dynamix/lolly/firmware/src/palette.h

TBlendType currentBlending;

uint8_t currentPaletteNumber = 0;
CRGBPalette16 currentPalette(CRGB::Black);
CRGBPalette16 targetPalette;

extern CRGBPalette16 myRedWhiteBluePalette;
extern const TProgmemPalette16 myRedWhiteBluePalette_p PROGMEM;

// This function fills the palette with totally random colors.
void SetupTotallyRandomPalette()
{
  for (int i = 0; i < 16; i++)
  {
    currentPalette[i] = CHSV(random8(), 255, random8());
  }
}

// This function sets up a palette of black and white stripes,
// using code.  Since the palette is effectively an array of
// sixteen CRGB colors, the various fill_* functions can be used
// to set them up.
void SetupBlackAndWhiteStripedPalette()
{
  // 'black out' all 16 palette entries...
  fill_solid(currentPalette, 16, CRGB::Black);
  // and set every fourth one to white.
  currentPalette[0] = CRGB::White;
  currentPalette[4] = CRGB::White;
  currentPalette[8] = CRGB::White;
  currentPalette[12] = CRGB::White;
}

// This function sets up a palette of purple and green stripes.
void SetupPurpleAndGreenPalette()
{
  CRGB purple = CHSV(HUE_PURPLE, 255, 255);
  CRGB green = CHSV(HUE_GREEN, 255, 255);
  CRGB black = CRGB::Black;

  currentPalette = CRGBPalette16(
      green, green, black, black,
      purple, purple, black, black,
      green, green, black, black,
      purple, purple, black, black);
}

void ChangePalettePeriodically()
{
  uint8_t secondHand = (millis() / 1000) % 60;
  static uint8_t lastSecond = 99;

  if (lastSecond != secondHand)
  {
    lastSecond = secondHand;
    if (secondHand == 0)
    {
      currentPalette = RainbowColors_p;
      currentBlending = LINEARBLEND;
    }
    if (secondHand == 10)
    {
      currentPalette = RainbowStripeColors_p;
      currentBlending = NOBLEND;
    }
    if (secondHand == 15)
    {
      currentPalette = RainbowStripeColors_p;
      currentBlending = LINEARBLEND;
    }
    if (secondHand == 20)
    {
      SetupPurpleAndGreenPalette();
      currentBlending = LINEARBLEND;
    }
    if (secondHand == 25)
    {
      SetupTotallyRandomPalette();
      currentBlending = LINEARBLEND;
    }
    if (secondHand == 30)
    {
      SetupBlackAndWhiteStripedPalette();
      currentBlending = NOBLEND;
    }
    if (secondHand == 35)
    {
      SetupBlackAndWhiteStripedPalette();
      currentBlending = LINEARBLEND;
    }
    if (secondHand == 40)
    {
      currentPalette = CloudColors_p;
      currentBlending = LINEARBLEND;
    }
    if (secondHand == 45)
    {
      currentPalette = PartyColors_p;
      currentBlending = LINEARBLEND;
    }
  }
}

// Gradient Color Palette definitions for 33 different cpt-city color palettes.
//     956 bytes of PROGMEM for all of the palettes together,
//    +618 bytes of PROGMEM for gradient palette code (AVR).
//   1,494 bytes total for all 34 color palettes and associated code.

// Gradient palette "ib_jul01_gp", originally from
// http://soliton.vm.bytemark.co.uk/pub/cpt-city/ing/xmas/tn/ib_jul01.png.index.html
// converted for FastLED with gammas (2.6, 2.2, 2.5)
// Size: 16 bytes of program space.

DEFINE_GRADIENT_PALETTE(ib_jul01_gp){
    0, 194, 1, 1,
    94, 1, 29, 18,
    132, 57, 131, 28,
    255, 113, 1, 1};

// Gradient palette "es_vintage_57_gp", originally from
// http://soliton.vm.bytemark.co.uk/pub/cpt-city/es/vintage/tn/es_vintage_57.png.index.html
// converted for FastLED with gammas (2.6, 2.2, 2.5)
// Size: 20 bytes of program space.

DEFINE_GRADIENT_PALETTE(es_vintage_57_gp){
    0, 2, 1, 1,
    53, 18, 1, 0,
    104, 69, 29, 1,
    153, 167, 135, 10,
    255, 46, 56, 4};

// Gradient palette "es_vintage_01_gp", originally from
// http://soliton.vm.bytemark.co.uk/pub/cpt-city/es/vintage/tn/es_vintage_01.png.index.html
// converted for FastLED with gammas (2.6, 2.2, 2.5)
// Size: 32 bytes of program space.

DEFINE_GRADIENT_PALETTE(es_vintage_01_gp){
    0, 4, 1, 1,
    51, 16, 0, 1,
    76, 97, 104, 3,
    101, 255, 131, 19,
    127, 67, 9, 4,
    153, 16, 0, 1,
    229, 4, 1, 1,
    255, 4, 1, 1};

// Gradient palette "es_rivendell_15_gp", originally from
// http://soliton.vm.bytemark.co.uk/pub/cpt-city/es/rivendell/tn/es_rivendell_15.png.index.html
// converted for FastLED with gammas (2.6, 2.2, 2.5)
// Size: 20 bytes of program space.

DEFINE_GRADIENT_PALETTE(es_rivendell_15_gp){
    0, 1, 14, 5,
    101, 16, 36, 14,
    165, 56, 68, 30,
    242, 150, 156, 99,
    255, 150, 156, 99};

// Gradient palette "rgi_15_gp", originally from
// http://soliton.vm.bytemark.co.uk/pub/cpt-city/ds/rgi/tn/rgi_15.png.index.html
// converted for FastLED with gammas (2.6, 2.2, 2.5)
// Size: 36 bytes of program space.

DEFINE_GRADIENT_PALETTE(rgi_15_gp){
    0, 4, 1, 31,
    31, 55, 1, 16,
    63, 197, 3, 7,
    95, 59, 2, 17,
    127, 6, 2, 34,
    159, 39, 6, 33,
    191, 112, 13, 32,
    223, 56, 9, 35,
    255, 22, 6, 38};

// Gradient palette "retro2_16_gp", originally from
// http://soliton.vm.bytemark.co.uk/pub/cpt-city/ma/retro2/tn/retro2_16.png.index.html
// converted for FastLED with gammas (2.6, 2.2, 2.5)
// Size: 8 bytes of program space.

DEFINE_GRADIENT_PALETTE(retro2_16_gp){
    0, 188, 135, 1,
    255, 46, 7, 1};

// Gradient palette "Analogous_1_gp", originally from
// http://soliton.vm.bytemark.co.uk/pub/cpt-city/nd/red/tn/Analogous_1.png.index.html
// converted for FastLED with gammas (2.6, 2.2, 2.5)
// Size: 20 bytes of program space.

DEFINE_GRADIENT_PALETTE(Analogous_1_gp){
    0, 3, 0, 255,
    63, 23, 0, 255,
    127, 67, 0, 255,
    191, 142, 0, 45,
    255, 255, 0, 0};

// Gradient palette "es_pinksplash_08_gp", originally from
// http://soliton.vm.bytemark.co.uk/pub/cpt-city/es/pink_splash/tn/es_pinksplash_08.png.index.html
// converted for FastLED with gammas (2.6, 2.2, 2.5)
// Size: 20 bytes of program space.

DEFINE_GRADIENT_PALETTE(es_pinksplash_08_gp){
    0, 126, 11, 255,
    127, 197, 1, 22,
    175, 210, 157, 172,
    221, 157, 3, 112,
    255, 157, 3, 112};

// Gradient palette "es_pinksplash_07_gp", originally from
// http://soliton.vm.bytemark.co.uk/pub/cpt-city/es/pink_splash/tn/es_pinksplash_07.png.index.html
// converted for FastLED with gammas (2.6, 2.2, 2.5)
// Size: 28 bytes of program space.

DEFINE_GRADIENT_PALETTE(es_pinksplash_07_gp){
    0, 229, 1, 1,
    61, 242, 4, 63,
    101, 255, 12, 255,
    127, 249, 81, 252,
    153, 255, 11, 235,
    193, 244, 5, 68,
    255, 232, 1, 5};

// Gradient palette "Coral_reef_gp", originally from
// http://soliton.vm.bytemark.co.uk/pub/cpt-city/nd/other/tn/Coral_reef.png.index.html
// converted for FastLED with gammas (2.6, 2.2, 2.5)
// Size: 24 bytes of program space.

DEFINE_GRADIENT_PALETTE(Coral_reef_gp){
    0, 40, 199, 197,
    50, 10, 152, 155,
    96, 1, 111, 120,
    96, 43, 127, 162,
    139, 10, 73, 111,
    255, 1, 34, 71};

// Gradient palette "es_ocean_breeze_068_gp", originally from
// http://soliton.vm.bytemark.co.uk/pub/cpt-city/es/ocean_breeze/tn/es_ocean_breeze_068.png.index.html
// converted for FastLED with gammas (2.6, 2.2, 2.5)
// Size: 24 bytes of program space.

DEFINE_GRADIENT_PALETTE(es_ocean_breeze_068_gp){
    0, 100, 156, 153,
    51, 1, 99, 137,
    101, 1, 68, 84,
    104, 35, 142, 168,
    178, 0, 63, 117,
    255, 1, 10, 10};

// Gradient palette "es_ocean_breeze_036_gp", originally from
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

DEFINE_GRADIENT_PALETTE(Pink_Purple_gp){
    0, 19, 2, 39,
    25, 26, 4, 45,
    51, 33, 6, 52,
    76, 68, 62, 125,
    102, 118, 187, 240,
    109, 163, 215, 247,
    114, 217, 244, 255,
    122, 159, 149, 221,
    149, 113, 78, 188,
    183, 128, 57, 155,
    255, 146, 40, 123};

// Gradient palette "Sunset_Real_gp", originally from
// http://soliton.vm.bytemark.co.uk/pub/cpt-city/nd/atmospheric/tn/Sunset_Real.png.index.html
// converted for FastLED with gammas (2.6, 2.2, 2.5)
// Size: 28 bytes of program space.

DEFINE_GRADIENT_PALETTE(Sunset_Real_gp){
    0, 120, 0, 0,
    22, 179, 22, 0,
    51, 255, 104, 0,
    85, 167, 22, 18,
    135, 100, 0, 103,
    198, 16, 0, 130,
    255, 0, 0, 160};

// Gradient palette "es_autumn_19_gp", originally from
// http://soliton.vm.bytemark.co.uk/pub/cpt-city/es/autumn/tn/es_autumn_19.png.index.html
// converted for FastLED with gammas (2.6, 2.2, 2.5)
// Size: 52 bytes of program space.

DEFINE_GRADIENT_PALETTE(es_autumn_19_gp){
    0, 26, 1, 1,
    51, 67, 4, 1,
    84, 118, 14, 1,
    104, 137, 152, 52,
    112, 113, 65, 1,
    122, 133, 149, 59,
    124, 137, 152, 52,
    135, 113, 65, 1,
    142, 139, 154, 46,
    163, 113, 13, 1,
    204, 55, 3, 1,
    249, 17, 1, 1,
    255, 17, 1, 1};

// Gradient palette "BlacK_Blue_Magenta_White_gp", originally from
// http://soliton.vm.bytemark.co.uk/pub/cpt-city/nd/basic/tn/BlacK_Blue_Magenta_White.png.index.html
// converted for FastLED with gammas (2.6, 2.2, 2.5)
// Size: 28 bytes of program space.

DEFINE_GRADIENT_PALETTE(BlacK_Blue_Magenta_White_gp){
    0, 0, 0, 0,
    42, 0, 0, 45,
    84, 0, 0, 255,
    127, 42, 0, 255,
    170, 255, 0, 255,
    212, 255, 55, 255,
    255, 255, 255, 255};

// Gradient palette "BlacK_Magenta_Red_gp", originally from
// http://soliton.vm.bytemark.co.uk/pub/cpt-city/nd/basic/tn/BlacK_Magenta_Red.png.index.html
// converted for FastLED with gammas (2.6, 2.2, 2.5)
// Size: 20 bytes of program space.

DEFINE_GRADIENT_PALETTE(BlacK_Magenta_Red_gp){
    0, 0, 0, 0,
    63, 42, 0, 45,
    127, 255, 0, 255,
    191, 255, 0, 45,
    255, 255, 0, 0};

// Gradient palette "BlacK_Red_Magenta_Yellow_gp", originally from
// http://soliton.vm.bytemark.co.uk/pub/cpt-city/nd/basic/tn/BlacK_Red_Magenta_Yellow.png.index.html
// converted for FastLED with gammas (2.6, 2.2, 2.5)
// Size: 28 bytes of program space.

DEFINE_GRADIENT_PALETTE(BlacK_Red_Magenta_Yellow_gp){
    0, 0, 0, 0,
    42, 42, 0, 0,
    84, 255, 0, 0,
    127, 255, 0, 45,
    170, 255, 0, 255,
    212, 255, 55, 45,
    255, 255, 255, 0};

// Gradient palette "Blue_Cyan_Yellow_gp", originally from
// http://soliton.vm.bytemark.co.uk/pub/cpt-city/nd/basic/tn/Blue_Cyan_Yellow.png.index.html
// converted for FastLED with gammas (2.6, 2.2, 2.5)
// Size: 20 bytes of program space.

DEFINE_GRADIENT_PALETTE(Blue_Cyan_Yellow_gp){
    0, 0, 0, 255,
    63, 0, 55, 255,
    127, 0, 255, 255,
    191, 42, 255, 45,
    255, 255, 255, 0};

const TProgmemRGBGradientPalettePtr gradientPalettes[] = {
    Sunset_Real_gp,
    es_rivendell_15_gp,
    es_ocean_breeze_036_gp,
    rgi_15_gp,
    retro2_16_gp,
    Analogous_1_gp,
    es_pinksplash_08_gp,
    Coral_reef_gp,
    es_ocean_breeze_068_gp,
    es_pinksplash_07_gp,
    es_vintage_01_gp,
    departure_gp,
    es_landscape_64_gp,
    es_landscape_33_gp,
    rainbowsherbet_gp,
    gr65_hult_gp,
    gr64_hult_gp,
    GMT_drywet_gp,
    ib_jul01_gp,
    es_vintage_57_gp,
    ib15_gp,
    Fuschia_7_gp,
    es_emerald_dragon_08_gp,
    lava_gp,
    fire_gp,
    Colorfull_gp,
    Magenta_Evening_gp,
    Pink_Purple_gp,
    es_autumn_19_gp,
    BlacK_Blue_Magenta_White_gp,
    BlacK_Magenta_Red_gp,
    BlacK_Red_Magenta_Yellow_gp,
    Blue_Cyan_Yellow_gp};

// Count of how many cpt-city gradients are defined:
const uint8_t gradientPaletteCount =
    sizeof(gradientPalettes) / sizeof(TProgmemRGBGradientPalettePtr);

extern const TProgmemRGBGradientPalettePtr gradientPalettes[];
extern const uint8_t gradientPaletteCount;
